nuclearfurnace/manual-pick-and-place/projects/vacuum-controller-rev-a/graphics/vacuum-controller-panel.bmp

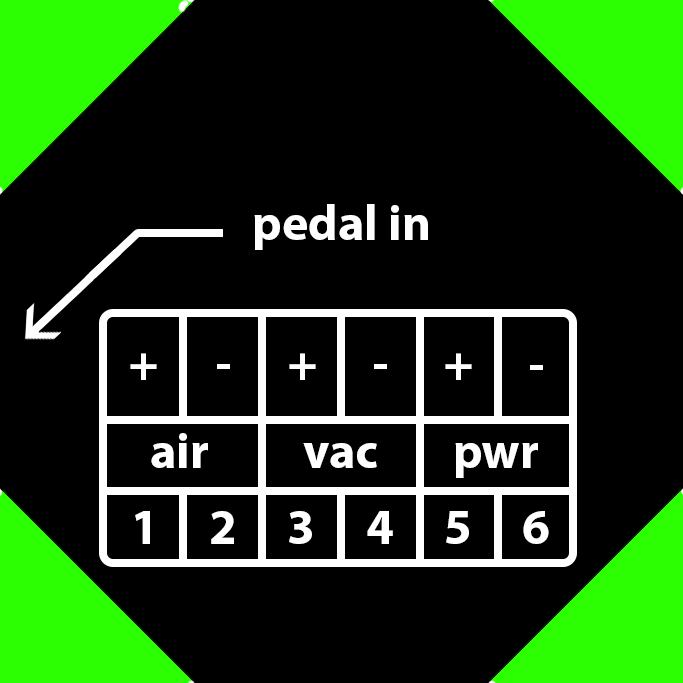
projects/vacuum-controller-rev-a/graphics/vacuum-controller-panel.bmp
