nuclearfurnace/manual-pick-and-place/place-bed.SLDPRT

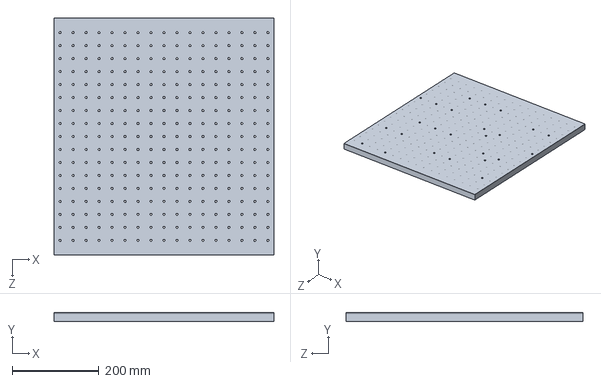
[picture p20: CAD file, 2017-05-13]
place-bed.SLDPRT
508.0 x 19.8 x 548.0 mm
