nuclearfurnace/manual-pick-and-place/components/cp40-nozzle-holder.SLDPRT

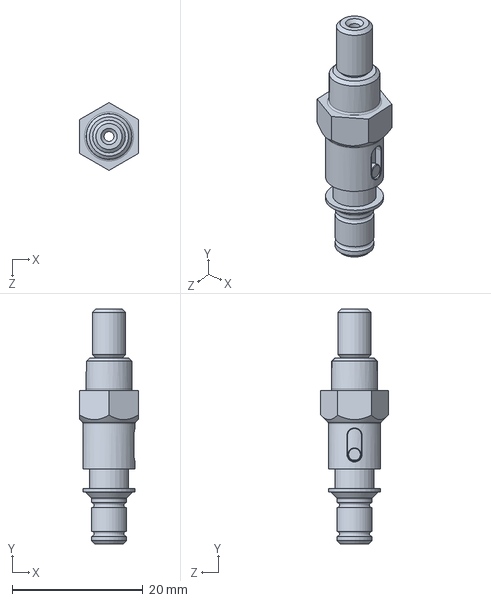
[picture p21: CAD file, 2017-04-17]
components/cp40-nozzle-holder.SLDPRT
9.00 x 36.0 x 10.4 mm
