nuclearfurnace/manual-pick-and-place/components/custom/rail-end-stops.SLDPRT

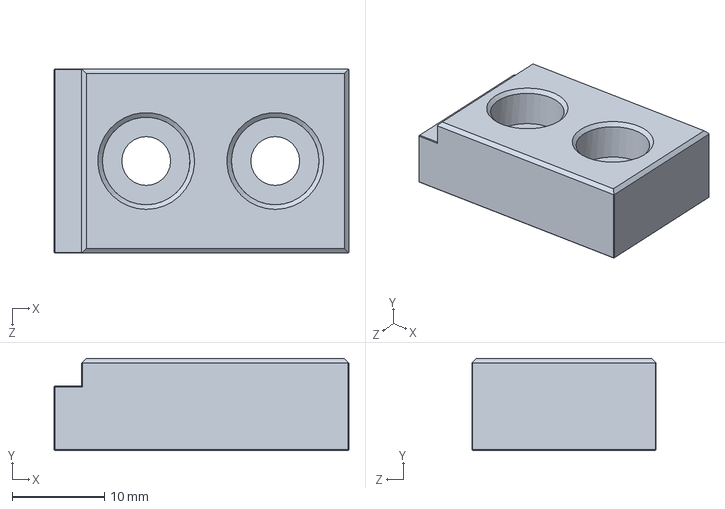
[picture p22: CAD file, 2017-05-03]
components/custom/rail-end-stops.SLDPRT
32.0 x 10.0 x 20.0 mm
