nuclearfurnace/manual-pick-and-place/projects/vacuum-controller-rev-a/enclosure/components/MJ-3536N.sldprt

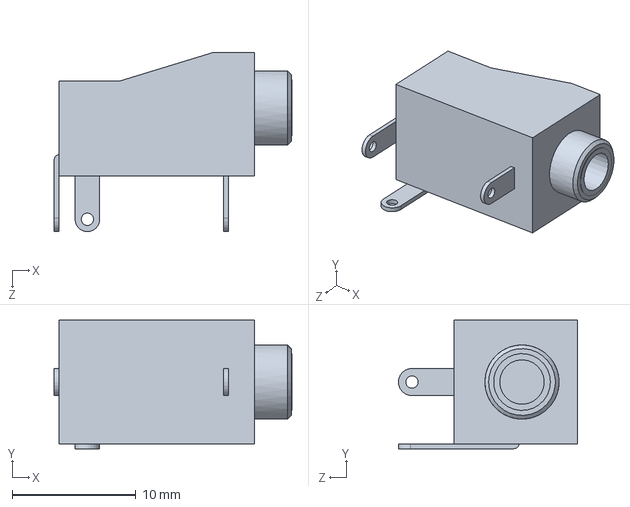
[picture p23: CAD file, 2017-05-04]
projects/vacuum-controller-rev-a/enclosure/components/MJ-3536N.sldprt
19.2 x 10.4 x 14.5 mm
