nuclearfurnace/manual-pick-and-place/components/custom/x-axis-bracket.SLDPRT

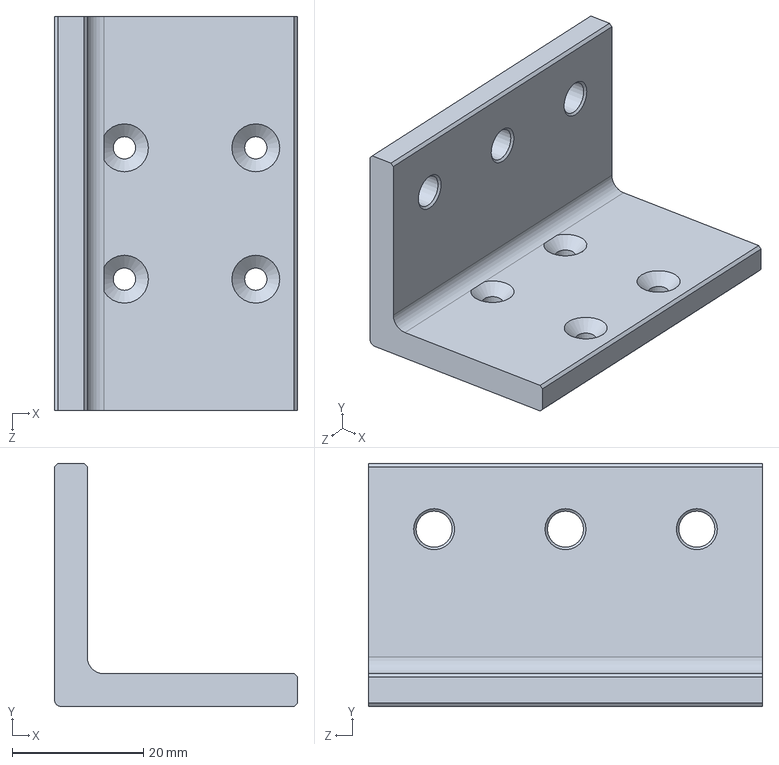
[picture p24: CAD file, 2017-04-17]
components/custom/x-axis-bracket.SLDPRT
37.0 x 37.0 x 60.0 mm
