nuclearfurnace/manual-pick-and-place/projects/vacuum-controller-rev-a/enclosure/components/LP-11F-bottom.SLDPRT

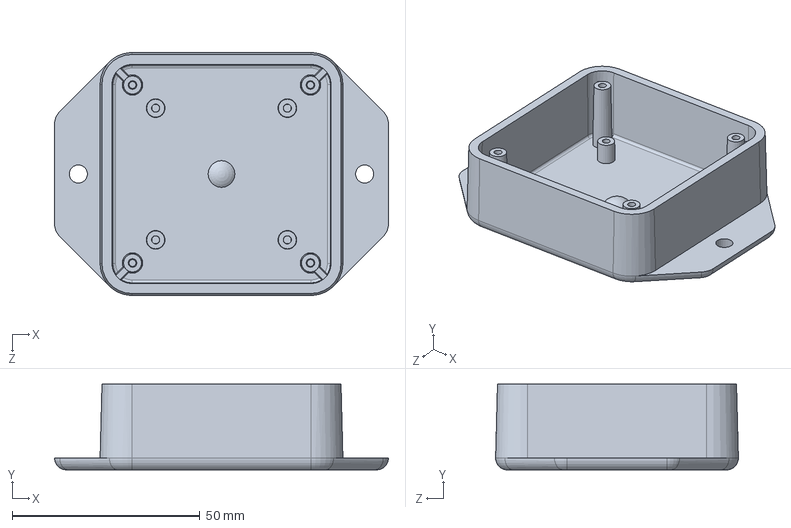
[picture p25: CAD file, 2017-05-04]
projects/vacuum-controller-rev-a/enclosure/components/LP-11F-bottom.SLDPRT
88.9 x 22.9 x 64.6 mm
