nuclearfurnace/manual-pick-and-place/components/custom/z-axis-bracket.SLDPRT

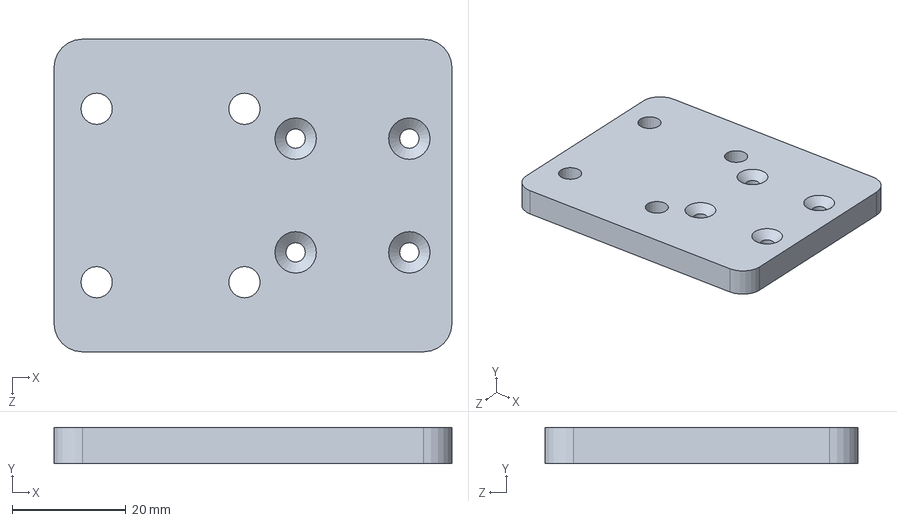
[picture p26: CAD file, 2017-04-15]
components/custom/z-axis-bracket.SLDPRT
70.0 x 6.35 x 55.0 mm
