nuclearfurnace/manual-pick-and-place/components/MGN_12_H_RAIL.SLDPRT

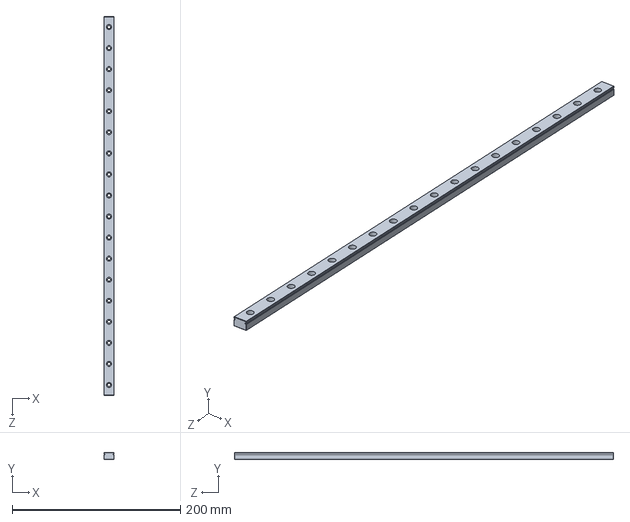
[picture p27: CAD file, 2017-04-17]
components/MGN_12_H_RAIL.SLDPRT
12.0 x 8.00 x 450.0 mm
