nuclearfurnace/manual-pick-and-place/components/HFC5-2060-B.sldprt

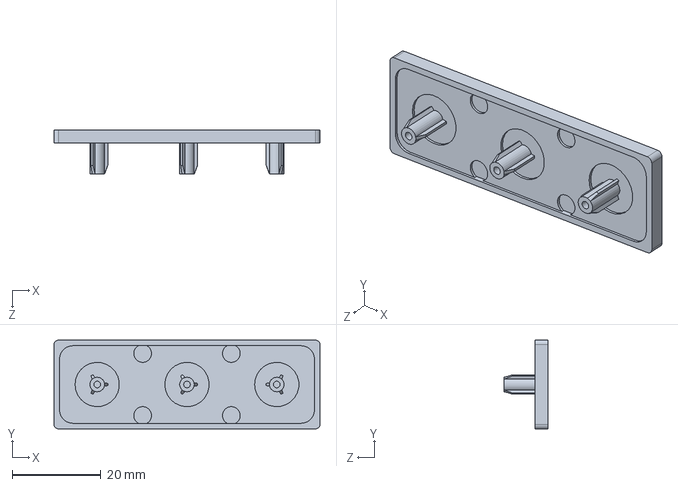
[picture p28: CAD file, 2017-04-17]
components/HFC5-2060-B.sldprt
60.0 x 20.0 x 10.0 mm
