nuclearfurnace/manual-pick-and-place/components/MGN_12_H_CARRAGE.SLDPRT

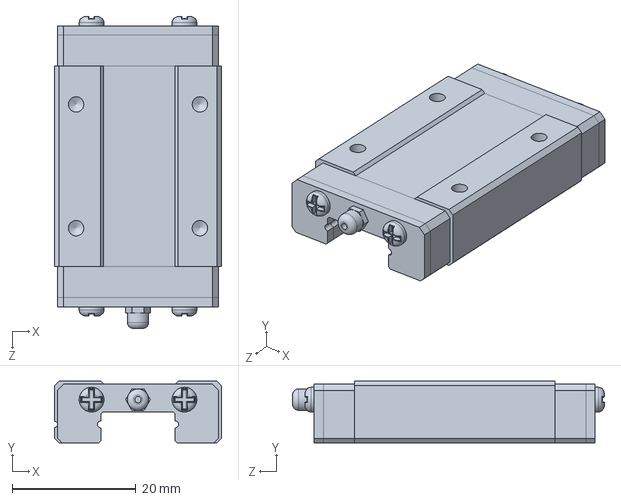
[picture p29: CAD file, 2017-04-17]
components/MGN_12_H_CARRAGE.SLDPRT
27.0 x 10.0 x 50.4 mm
