nuclearfurnace/manual-pick-and-place/components/HNTT5-5.sldprt

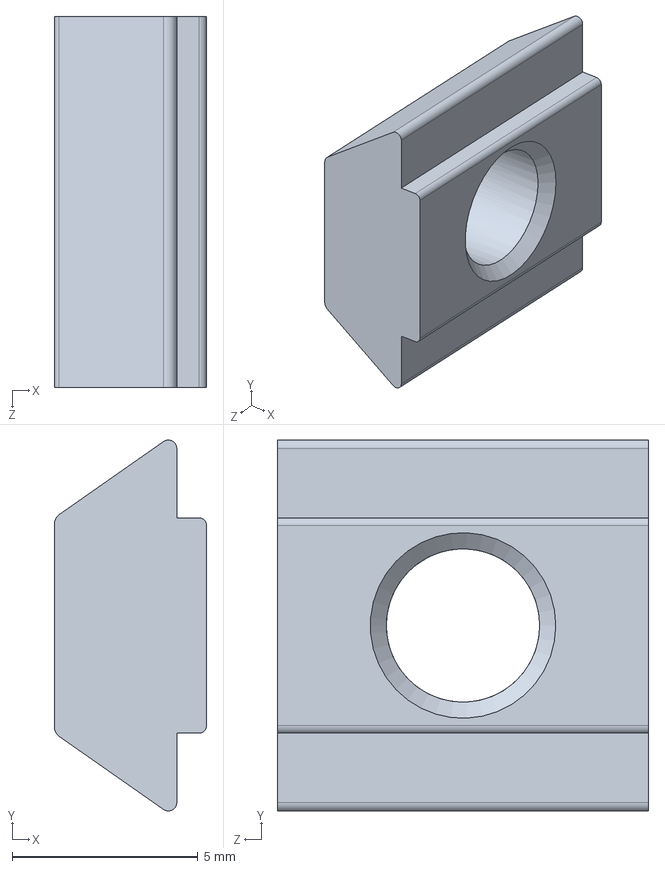
[picture p30: CAD file, 2017-04-17]
components/HNTT5-5.sldprt
4.10 x 10.00 x 10.0 mm
