nuclearfurnace/manual-pick-and-place/components/RTCNL4-M5.sldprt

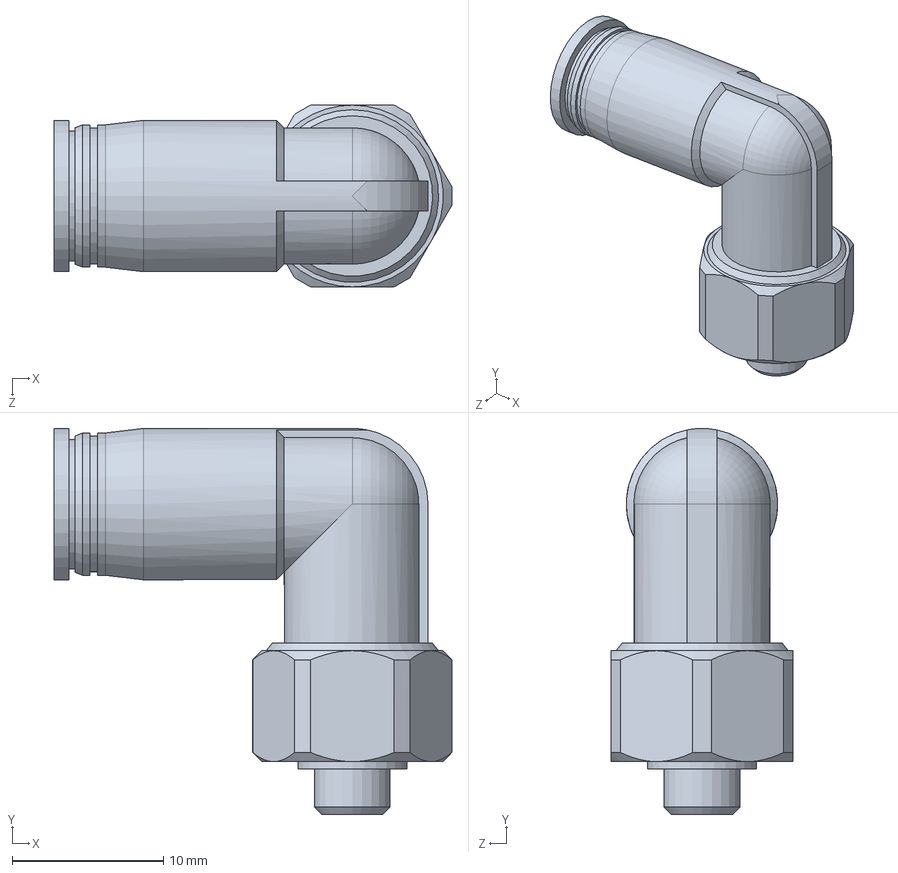
[picture p31: CAD file, 2017-04-17]
components/RTCNL4-M5.sldprt
26.3 x 25.5 x 12.0 mm
