nuclearfurnace/manual-pick-and-place/components/HFS5-2060-130-Z5-YA10.sldprt

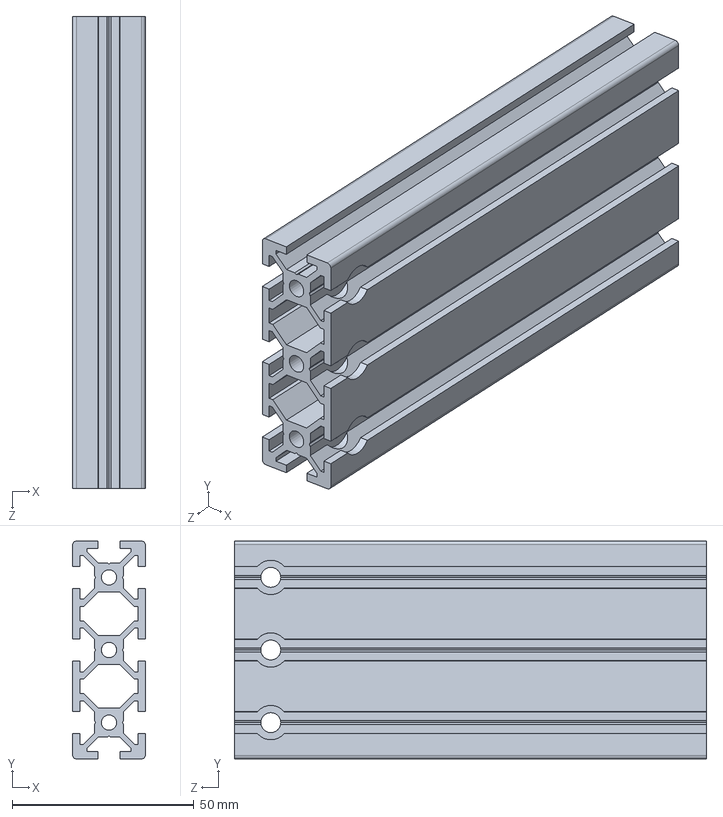
[picture p33: CAD file, 2017-04-15]
components/HFS5-2060-130-Z5-YA10.sldprt
20.0 x 60.0 x 130.0 mm
