nuclearfurnace/manual-pick-and-place/components/HFS5-2060-600.sldprt

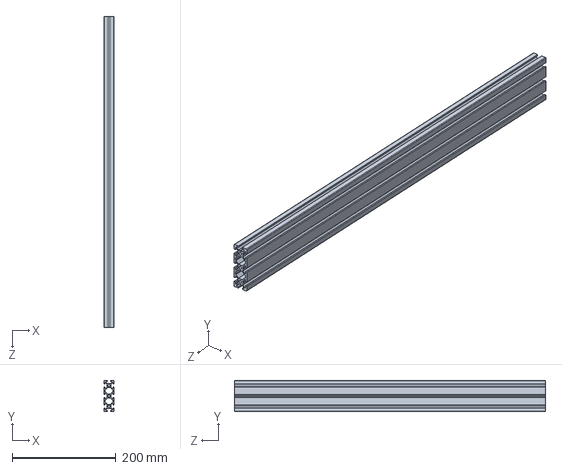
[picture p34: CAD file, 2017-04-15]
components/HFS5-2060-600.sldprt
20.0 x 60.0 x 600.0 mm
