nuclearfurnace/manual-pick-and-place/components/HFS5-2040-550.sldprt

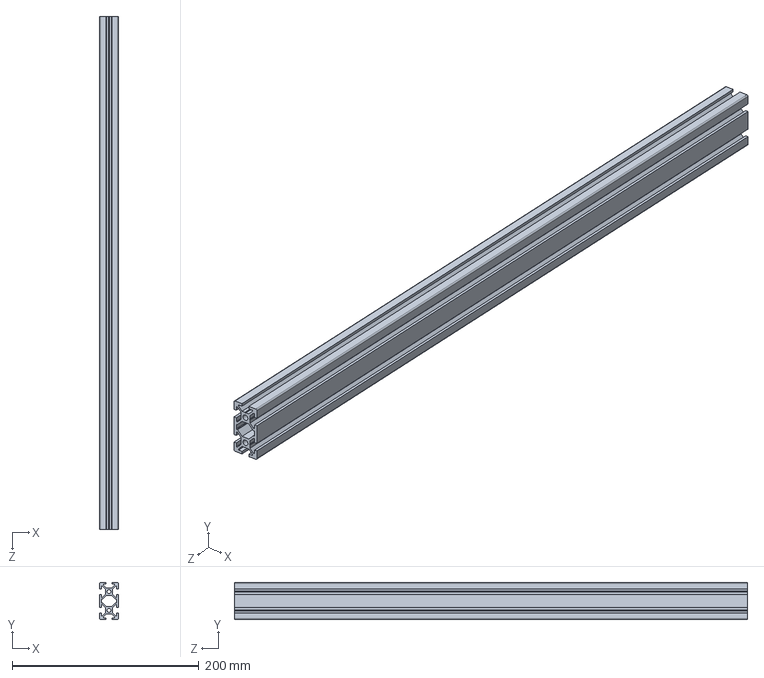
[picture p35: CAD file, 2017-04-15]
components/HFS5-2040-550.sldprt
20.0 x 40.0 x 550.0 mm
