nuclearfurnace/manual-pick-and-place/components/cp40-test-nozzle.SLDPRT

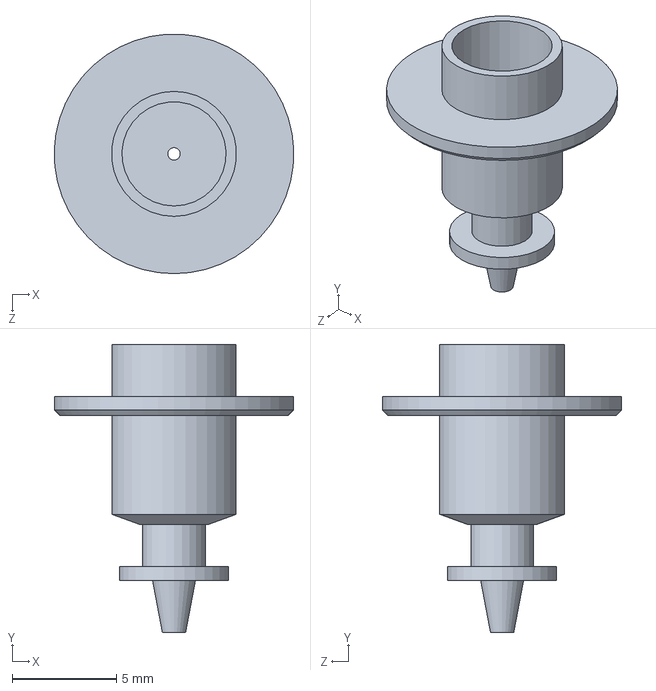
[picture p36: CAD file, 2017-04-15]
components/cp40-test-nozzle.SLDPRT
11.5 x 13.8 x 11.5 mm
