nuclearfurnace/manual-pick-and-place/components/LMU-N12.sldprt

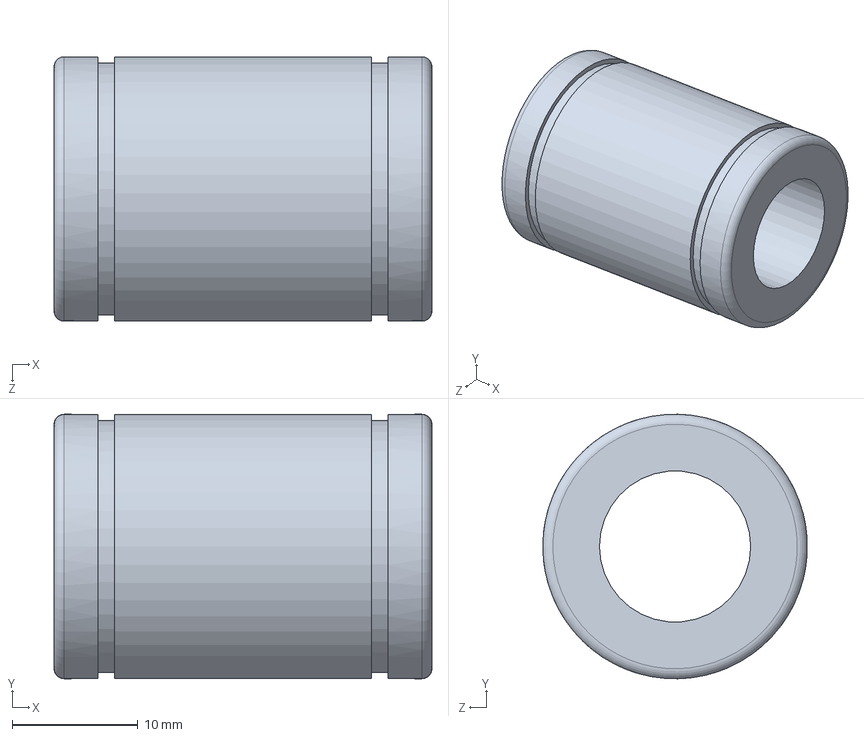
[picture p37: CAD file, 2017-04-14]
components/LMU-N12.sldprt
30.0 x 21.0 x 21.0 mm
