nuclearfurnace/manual-pick-and-place/components/LH-RRING-C-INT-S-21.sldprt

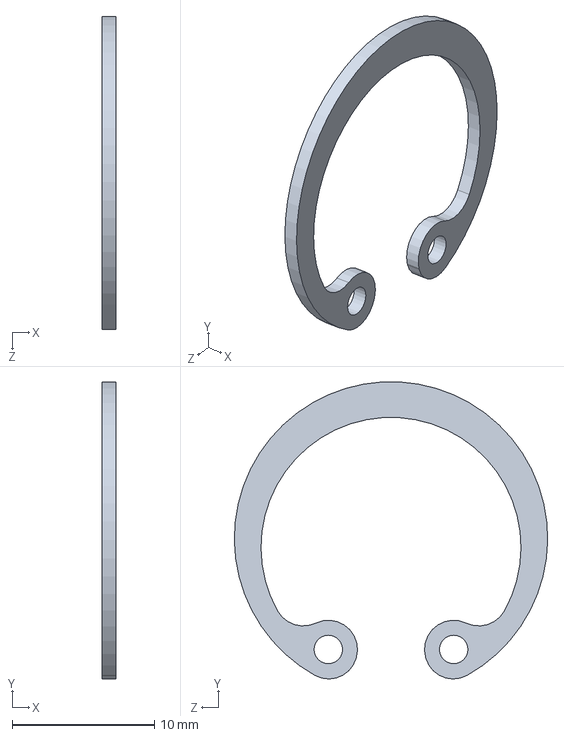
[picture p38: CAD file, 2017-04-14]
components/LH-RRING-C-INT-S-21.sldprt
1.00 x 20.8 x 22.0 mm
