nuclearfurnace/manual-pick-and-place/components/LHBB12-1_b.sldprt

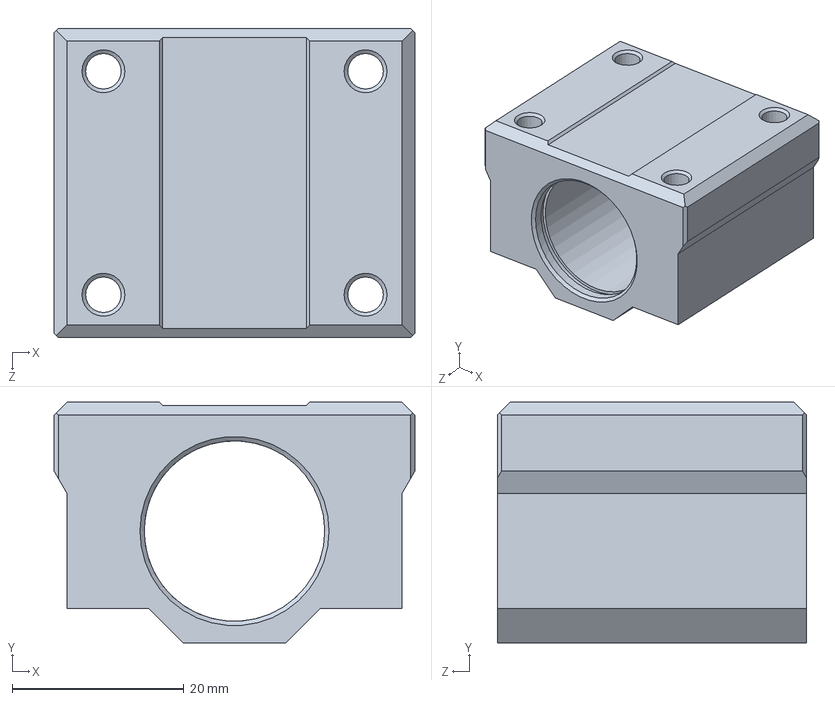
[picture p39: CAD file, 2017-04-14]
components/LHBB12-1_b.sldprt
42.0 x 28.0 x 36.0 mm
